JakeBoothy/PhotoSpectrometer-Electrical/V2/Eagle/LTSpice/amp_test.asc

R1: res; 10k
R2: res; 2408
R3: res; 201
R4: res; 600
R5: res; 100k
R6: res; 2.7k
R7: res; 10k
R8: res; 500
R9: res; 1.7k
R10: res; 100k
U1: ADA4807
U2: ADA4807
U3: ADA4807
V1: voltage; 5
V2: voltage; -5
V3: voltage; SINE(1.55 0.95 2e4)
V4: voltage; 2.5
Named nets: 0, +5, -5, +2.5
.tran 1
