JakeBoothy/PhotoSpectrometer-Electrical/V2/Eagle/LTSpice/CurrentSense.asc

R1: res; 10k
R2: res; 60k
R3: res; 2k
R4: res; 60k
R5: res; 0.05
R6: res; 2.5
U1: LM358
V1: voltage; 3.3
V2: voltage; PWL(0 0 1 20)
Named nets: 0, 3.3V, 12V
.tran 1
.inc LM358.MOD
