JakeBoothy/PhotoSpectrometer-Electrical/V2/Eagle/LTSpice/Draft2.asc

C1: cap; 200nF
M1: nmos; IRF8721
Q1: npn
R1: res; 51k
R2: res; 51k
R3: res; 10
V1: voltage; PULSE(0 36 0 0 0 0.05 0.1 10)
V2: voltage; 3.7
V3: voltage; 12V
Named nets: 0, 3.7V, 12V
.tran 1
