JakeBoothy/PhotoSpectrometer-Electrical/V2/Eagle/LTSpice/Draft3.asc

2.5k: res; 25k
R2: res; 10k
R3: res; 100k
R4: res; 80k
U1: UniversalOpamp2
V1: voltage; 2.5
V2: voltage; -2.5
V3: voltage; SINE(1.55 0.95 1E3)
Named nets: 0, +2.5V, -2.5V
.tran 1e-2
