JakeBoothy/PhotoSpectrometer-Electrical/V2/Eagle/LTSpice/Pelt_Driver.asc

C1: cap; 47µ
D1: diode
L1: ind; 100µ
M1: nmos; Si7336ADP
R1: res; 2.5
V1: voltage; 12V
V2: voltage; PULSE(0 3.3 0 0 0 0.00005 0.0001)
Named nets: 0
.tran 0.01
