JakeBoothy/PhotoSpectrometer-Electrical/V2/LTSPICE/LM358/Draft1.asc

R2: res; 10k
R3: res; 10k
U1: LM358
V1: voltage; 5
V2: voltage; SINE(1.5 1 5)
Named nets: 0
.tran 1
.inc LM358.MOD
