JakeBoothy/PhotoSpectrometer-Electrical/V2/Eagle/LTSpice/Draft1.asc

Q1: npn; 2SCR514P
R1: res; 51k
R2: res; 51k
R3: res; 120k
V1: voltage; PULSE(0 36 0 0 0 0.05 0.1)
V2: voltage; 4.2
Named nets: 0
.tran 0.2
