JakeBoothy/PhotoSpectrometer-Electrical/V2/Eagle/ccd_driver.sch

## EAGLE design V2/Eagle/ccd_driver.sch (2018-10-21)

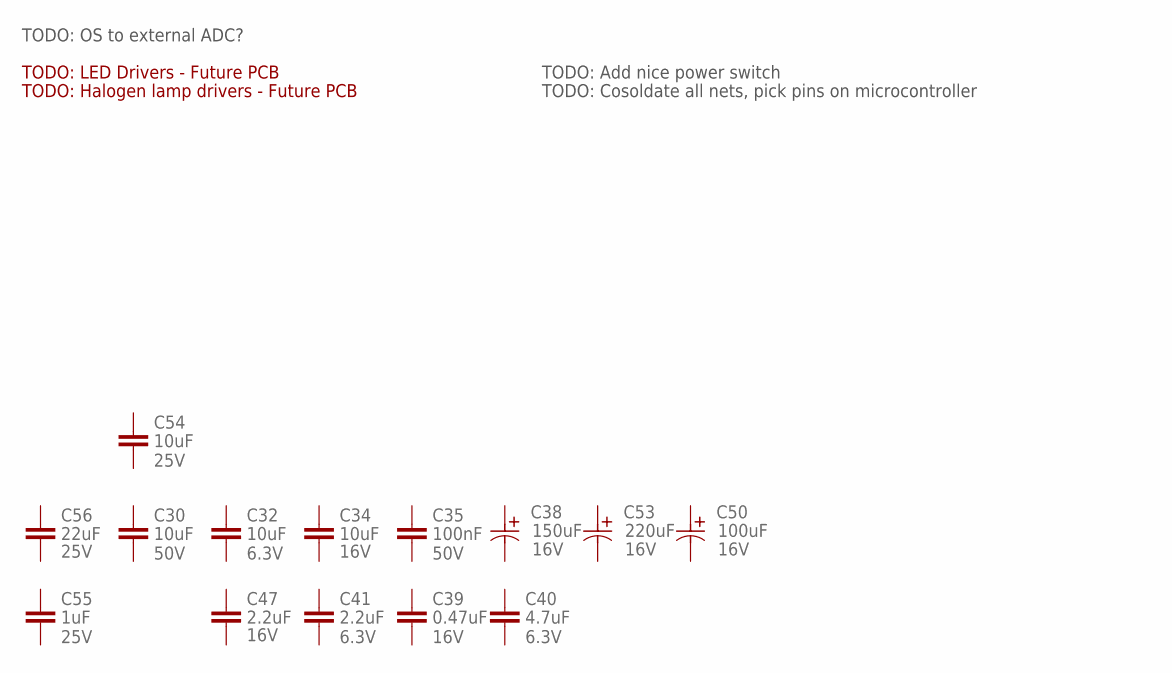
[picture p5: schematic ccd_driver.sch, sheet 1]

Parts:
C30: 10uF; C1206; VOLTAGE 50V; PARTNO 490-12456-1-ND
C32: 10uF; 0603-CAP; VOLTAGE 6.3V; PARTNO 1276-1119-1-ND
C34: 10uF; C0805; VOLTAGE 16V; PARTNO 1276-1096-1-ND
C35: 100nF; 0603-CAP; VOLTAGE 50V; PARTNO 311-1343-1-ND
C38: UWZ1C151MCL1GS; PCAP_6.3X7.7-ELECT; VOLTAGE 16V
C39: 0.47uF; 0603-CAP; VOLTAGE 16V; PARTNO 1276-1062-1-ND
C40: 4.7uF; 0603-CAP; VOLTAGE 6.3V; PARTNO 1276-1045-1-ND
C41: 2.2uF; 0603-CAP; VOLTAGE 6.3V; PARTNO 445-6933-1-ND
C47: 2.2uF; C0805; VOLTAGE 16V; PARTNO 1276-2957-1-ND
C50: EMVE160ADA101MF55G; PCAP_6.3X7.7-ELECT; VOLTAGE 16V
C53: UWZ1C151MCL1GS; PCAP_6.3X7.7-ELECT; VOLTAGE 16V; MANUFACTURER_PART_NUMBER UWT1C221MCL1GS
C54: 10uF; C1206; VOLTAGE 25V; PARTNO 1276-1075-1-ND
C55: 1uF; 0603-CAP; VOLTAGE 25V; PARTNO 1276-1102-1-ND
C56: 22uF; C0805; VOLTAGE 25V; PARTNO 490-12389-1-ND

Notes on the sheet:
TODO: OS to external ADC?
TODO: LED Drivers - Future PCB
TODO: Halogen lamp drivers - Future PCB
TODO: Add nice power switch
TODO: Cosoldate all nets, pick pins on microcontroller

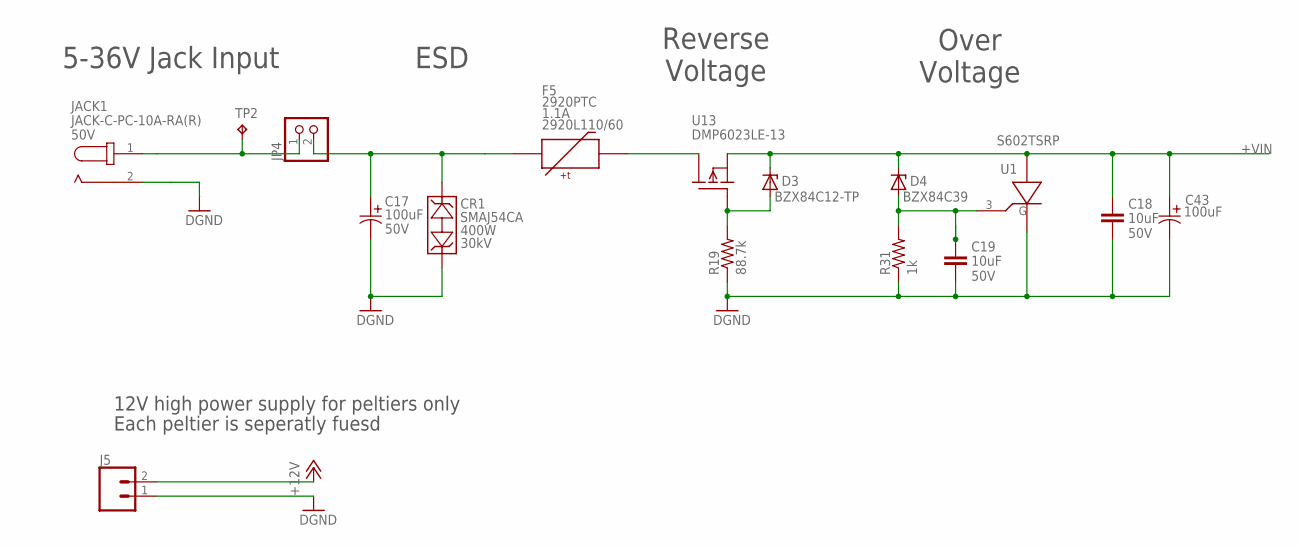
[picture p6: schematic ccd_driver.sch, sheet 2]

Parts:
C17: UWT1H101MNL1GS; PCAP_8X10-ELECT; VOLTAGE 50V
C18, C19: 10uF; C1206; VOLTAGE 50V; PARTNO 490-12456-1-ND
C43: UWT1H101MNL1GS; PCAP_8X10-ELECT
CR1: SMAJ54CA; SMASERIES
D3: BZX84C12-TP; SOT23
D4: BZX84C39; SOT23
F5: 2920PTC; 2920; PARTNO 2920L110/60
J5: CONN_023.5MM; SCREWTERMINAL-3.5MM-2
JACK1: JACK-C-PC-10A-RA(R); 1939-1086-ND
JP4: PINHD-1X2; 1X02
R19: 88.7k; R0603
R31: 1k; R0603
TP2: TPPAD1-13; P1-13
U1: S602TSRP; SOT223
U13: DMP6023LE-13; SOT-223

Connections:
+12V: J5.2
+VIN: C18.1, C43.1 (11), D3.3 (C), D4.3 (C), U1.2 (A), U13.3 (S)
GND: C17.2 (22), C18.2, C19.2, C43.2 (22), CR1.2 (1), J5.1, JACK1.2, R19.1, R31.1, U1.1 (K)
unnamed: C17.1 (11), CR1.1 (2), F5.P$2, JP4.2
unnamed: JACK1.1, JP4.1, TP2.TP
unnamed: F5.P$1, U13.2 (D)
unnamed: D3.1 (A), R19.2, U13.1 (G)
unnamed: C19.1, D4.1 (A), R31.2, U1.3 (G)

Notes on the sheet:
ESD
Reverse Voltage
Over Voltage
Each peltier is seperatly fuesd
5-36V Jack Input
12V high power supply for peltiers only

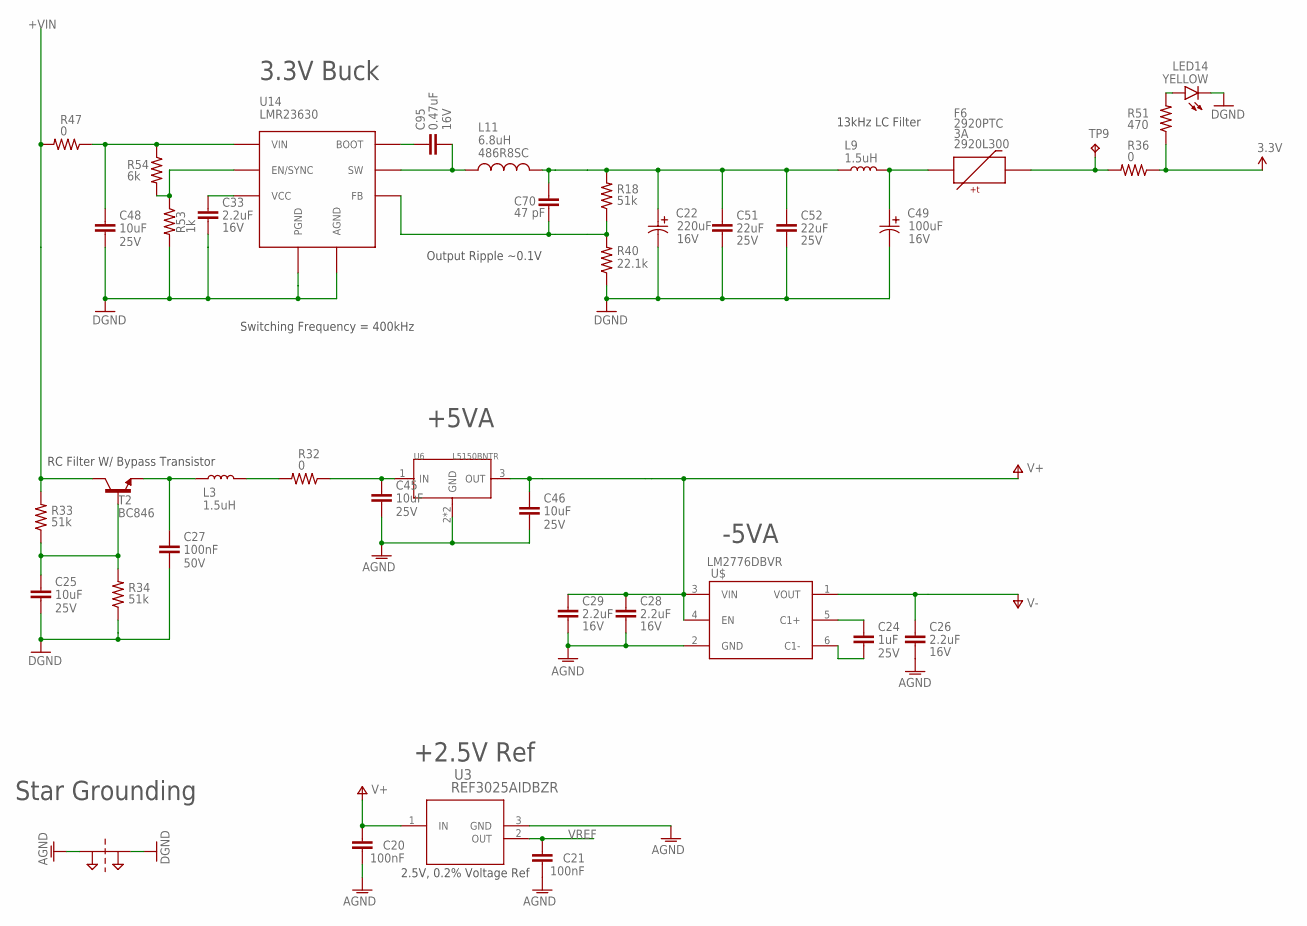
[picture p7: schematic ccd_driver.sch, sheet 3]

Parts:
C20, C21: 100nF; 0603-CAP
C22: UWZ1C151MCL1GS; PCAP_6.3X7.7-ELECT; VOLTAGE 16V; MANUFACTURER_PART_NUMBER UWT1C221MCL1GS
C24: 1uF; 0603-CAP; VOLTAGE 25V; PARTNO 1276-1102-1-ND
C25, C45, C46, C48: 10uF; C1206; VOLTAGE 25V; PARTNO 1276-1075-1-ND
C26, C28, C29, C33: 2.2uF; C0805; VOLTAGE 16V; PARTNO 1276-2957-1-ND
C27: 100nF; 0603-CAP; VOLTAGE 50V; PARTNO 311-1343-1-ND
C49: EMVE160ADA101MF55G; PCAP_6.3X7.7-ELECT; VOLTAGE 16V
C51, C52: 22uF; C0805; VOLTAGE 25V; PARTNO 490-12389-1-ND
C70: 47 pF; 0603-CAP
C95: 0.47uF; 0603-CAP; VOLTAGE 16V; PARTNO 1276-1062-1-ND
F6: 2920PTC; 2920; PARTNO 2920L300
L3, L9: CIGW252010GLR47MNE; 2520
L11: 486R8SC
LED14: SML-LX23; 3X2SMDLED
R18, R33, R34: 51k; R0603
R32, R36, R47: 0; R0603
R40: 22.1k; R0603
R51: 470; R0603
R53: 1k; R0603
R54: 6k; R0603
SUPPLY21: 2PT_GND_TIE
T2: BC846; SOT23
TP9: TPPAD1-13; P1-13
U3: REF3025AIDBZR; DBZ3
U6: L5150BNTR; SOT-223
U14: LMR23630; HSOIC-8
U$: LM2776DBVR; SOT23-6

Connections:
3.3V: R36.1, R51.1
+VIN: R33.2, R47.2, T2.3 (C)
AGND: C20.2, C21.2, C26.2, C28.2, C29.2, C45.2, C46.2, SUPPLY21.P$1, U3.3 (GND), U6.2 (GND), U$.2 (GND)
GND: C22.2 (22), C25.2, C27.2, C33.2, C48.2, C49.2 (22), C51.2, C52.2, LED14.C, R34.1, R40.1, R53.2, SUPPLY21.P$2, U14.P$6 (AGND), U14.P$8 (PGND)
unnamed: C45.1, R32.1, U6.1 (IN)
unnamed: L3.2, R32.2
unnamed: C25.1, R33.1, R34.2, T2.1 (B)
unnamed: C27.1, L3.1, T2.2 (E)
unnamed: C33.1, U14.P$3 (VCC)
unnamed: R53.1, R54.2, U14.P$5 (EN/SYNC)
unnamed: C48.1, R47.1, R54.1, U14.P$7 (VIN)
unnamed: C70.2, R18.1, R40.2, U14.P$4 (FB)
unnamed: C95.2, L11.P$1 (1), U14.P$1 (SW)
unnamed: C95.1, U14.P$2 (BOOT)
unnamed: C22.1 (11), C51.1, C52.1, C70.1, L9.1, L11.P$2 (2), R18.2
unnamed: F6.P$1, R36.2, TP9.TP
unnamed: LED14.A, R51.2
unnamed: C24.1, U$.5 (C1+)
unnamed: C24.2, U$.6 (C1-)
unnamed: C49.1 (11), F6.P$2, L9.2
V+: C20.1, C28.1, C29.1, C46.1, U3.1 (IN), U6.3 (OUT), U$.3 (VIN), U$.4 (EN)
V-: C26.1, U$.1 (VOUT)
VREF: C21.1, U3.2 (OUT)

Notes on the sheet:
2.5V, 0.2% Voltage Ref
13kHz LC Filter
Output Ripple ~0.1V
Switching Frequency = 400kHz
RC Filter W/ Bypass Transistor
3.3V Buck
+5VA
-5VA
+2.5V Ref
Star Grounding

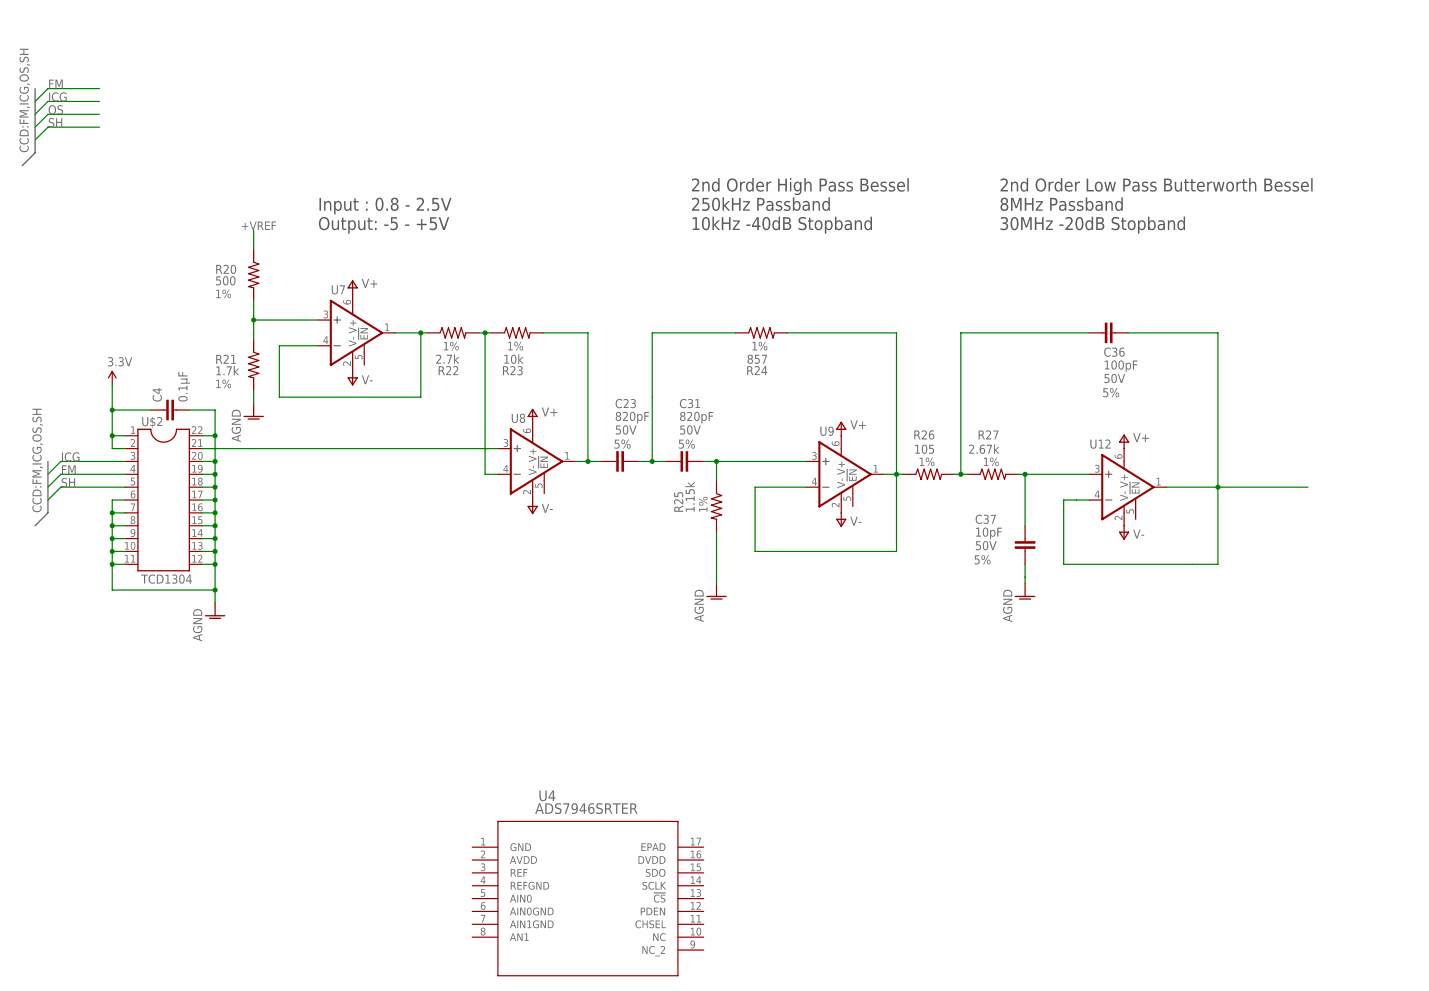
[picture p8: schematic ccd_driver.sch, sheet 4]

Parts:
C4: 0.1µF; C1206
C23, C31: 820pF; 0603-CAP; TOLERANCE 5%; VOLTAGE 50V; PARTNO 311-1343-1-ND
C36: 100pF; 0603-CAP; TOLERANCE 5%; VOLTAGE 50V; PARTNO 311-1343-1-ND
C37: 10pF; 0603-CAP; TOLERANCE 5%; VOLTAGE 50V; PARTNO 311-1343-1-ND
R20: 500; R0603; TOLERANCE 1%
R21: 1.7k; R0603; TOLERANCE 1%
R22: 2.7k; R0603; TOLERANCE 1%
R23: 10k; R0603; TOLERANCE 1%
R24: 857; R0603; TOLERANCE 1%
R25: 1.15k; R0603; TOLERANCE 1%
R26: 105; R0603; TOLERANCE 1%
R27: 2.67k; R0603; TOLERANCE 1%
U4: ADS7946SRTER; RTE16_1P7X1P7
U7, U8, U9, U12: ADA4807-1ARJZ-R2; RJ_6
U$2: TCD1304

Connections:
3.3V: C4.1, U$2.1, U$2.2
+VREF: R20.1
AGND: C4.2, C37.1, R21.2, R25.2, U$2.6, U$2.7, U$2.8, U$2.9, U$2.10, U$2.11, U$2.12, U$2.13, U$2.14, U$2.15, U$2.16, U$2.17, U$2.18, U$2.19, U$2.20, U$2.22
FM: U$2.4
ICG: U$2.3
unnamed: U8.3 (+IN), U$2.21
unnamed: R20.2, R21.1, U7.3 (+IN)
unnamed: R22.1, U7.1 (OUT), U7.4 (-IN)
unnamed: R22.2, R23.1, U8.4 (-IN)
unnamed: C23.1, R23.2, U8.1 (OUT)
unnamed: C23.2, C31.1, R24.1
unnamed: C31.2, R25.1, U9.3 (+IN)
unnamed: R24.2, R26.1, U9.1 (OUT), U9.4 (-IN)
unnamed: C37.2, R27.2, U12.3 (+IN)
unnamed: C36.1, R26.2, R27.1
unnamed: C36.2, U12.1 (OUT), U12.4 (-IN)
SH: U$2.5
V+: U7.6 (V+), U8.6 (V+), U9.6 (V+), U12.6 (V+)
V-: U7.2 (V-), U8.2 (V-), U9.2 (V-), U12.2 (V-)

Notes on the sheet:
Input : 0.8 - 2.5V Output: -5 - +5V
2nd Order High Pass Bessel 250kHz Passband 10kHz -40dB Stopband
2nd Order Low Pass Butterworth Bessel 8MHz Passband 30MHz -20dB Stopband

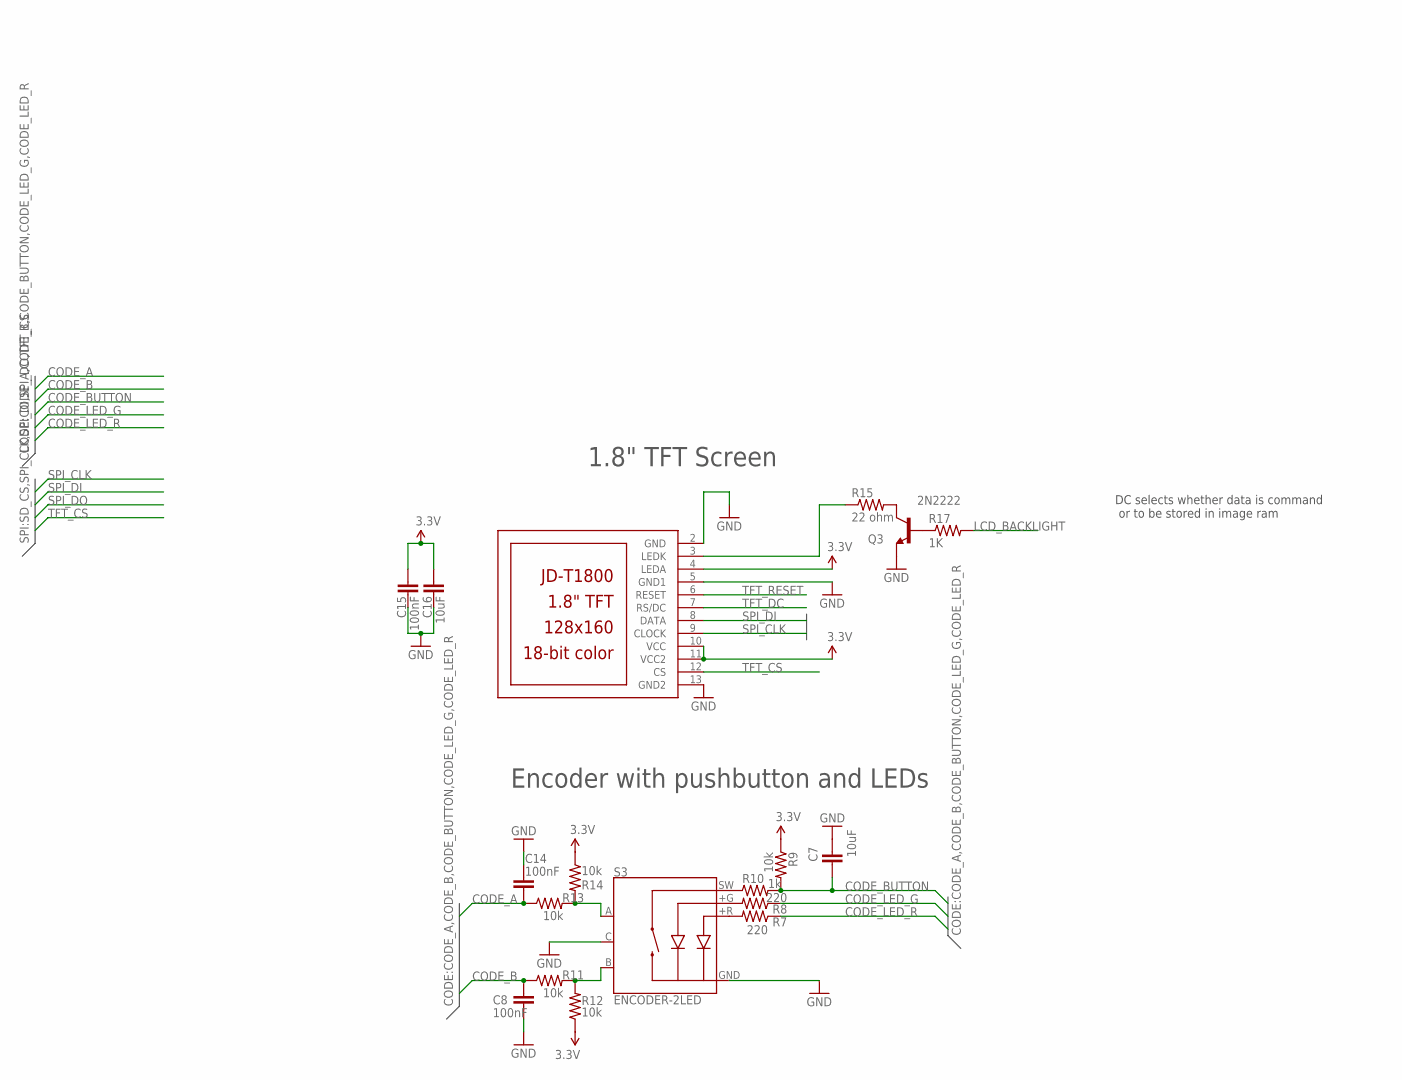
[picture p9: schematic ccd_driver.sch, sheet 5]

Parts:
C7, C16: 10uF; 0603-CAP
C8, C14, C15: 100nF; 0603-CAP
Q3: 2N2222; SOT23-BEC
R7, R8: 220; R0603
R9, R11, R12, R13, R14: 10k; R0603
R10: 1k; R0603
R15: 22 ohm; R0805
R17: 1K; R0805
S3: ENCODER-2LED; ENCODER_LED_2
U$10: JD-T1800

Connections:
3.3V: C15.1, C16.1, R9.1, R12.1, R14.1, U$10.4 (LEDA), U$10.10 (VCC), U$10.11 (VCC2)
CODE_A: C14.2, R13.1
CODE_B: C8.1, R11.1
CODE_BUTTON: C7.2, R9.2, R10.2
CODE_LED_G: R8.1
CODE_LED_R: R7.1
GND: C7.1, C8.2, C14.1, C15.2, C16.2, Q3.E, S3.C, S3.GND (-), U$10.2 (GND), U$10.5 (GND1), U$10.13 (GND2)
LCD_BACKLIGHT: R17.2
unnamed: R7.2, S3.+R
unnamed: R8.2, S3.+G
unnamed: R10.1, S3.SW
unnamed: R13.2, R14.2, S3.A
unnamed: R11.2, R12.2, S3.B
unnamed: R15.1, U$10.3 (LEDK)
unnamed: Q3.C, R15.2
unnamed: Q3.B, R17.1
SPI_CLK: U$10.9 (CLOCK)
SPI_DI: U$10.8 (DATA)
TFT_CS: U$10.12 (CS)
TFT_DC: U$10.7 (RS/DC)
TFT_RESET: U$10.6 (RESET)

Notes on the sheet:
DC selects whether data is command or to be stored in image ram
1.8" TFT Screen
Encoder with pushbutton and LEDs

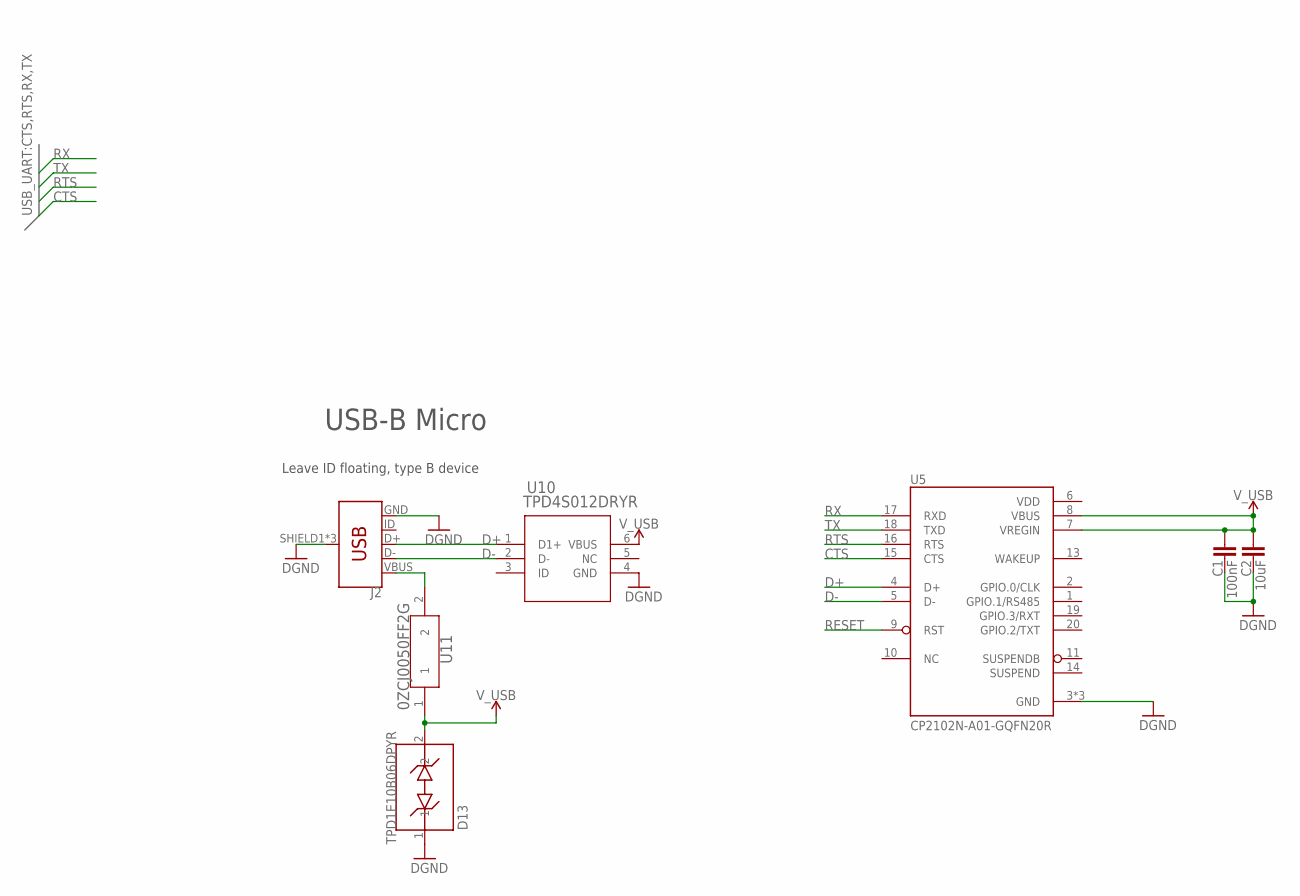
[picture p10: schematic ccd_driver.sch, sheet 6]

Parts:
C1: 100nF; 0603-CAP
C2: 10uF; 0603-CAP
D13: TPD1E10B06DPYR; DFN100X60X45-2N
J2: USB_MICRO-B_FEMALE-SMT; USB-B-MICRO-SMD
U5: CP2102N-A01-GQFN20R; SILABS_QFN20
U10: TPD4S012DRYR; DRY6
U11: 0ZCJ0050FF2G; 0ZCJ

Connections:
CTS: U5.15 (CTS)
D+: J2.D+, U5.4 (D+), U10.1 (D1+)
D-: J2.D-, U5.5 (D-), U10.2 (D-)
GND: C1.2, C2.2, D13.1, J2.GND, J2.SHIELD1 (SHIELD), U5.3 (GND), U10.4 (GND)
unnamed: J2.VBUS, U11.2
RESET: U5.9 (RST)
RTS: U5.16 (RTS)
RX: U5.17 (RXD)
TX: U5.18 (TXD)
V_USB: C1.1, C2.1, D13.2, U5.7 (VREGIN), U5.8 (VBUS), U10.6 (VBUS), U11.1

Notes on the sheet:
Leave ID floating, type B device
USB-B Micro

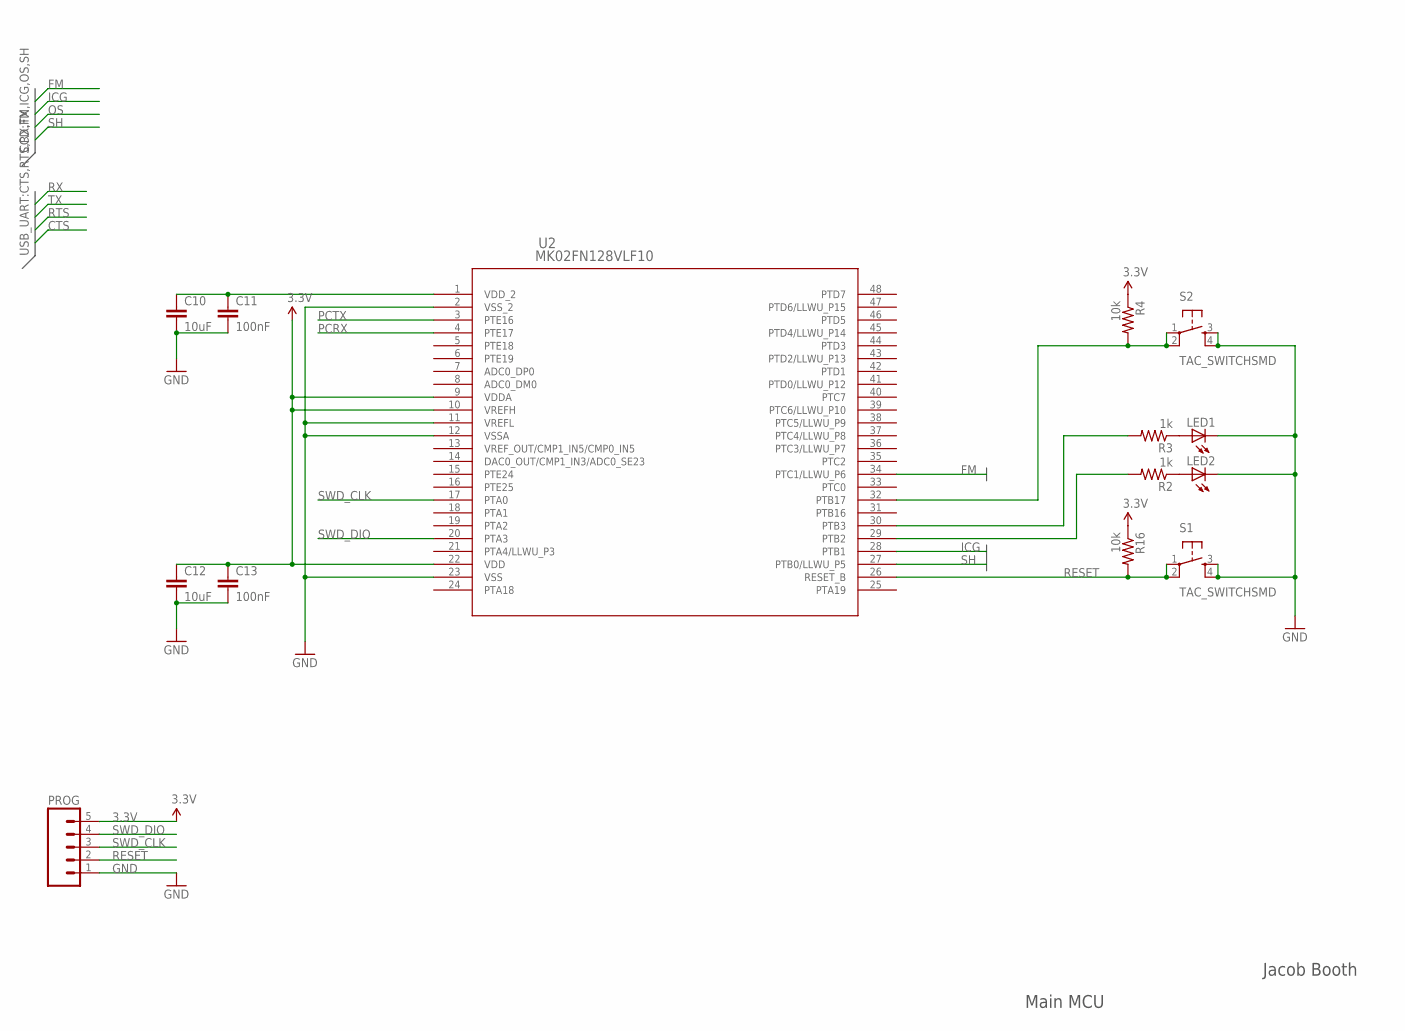
[picture p11: schematic ccd_driver.sch, sheet 7]

Parts:
C10, C12: 10uF; 0603
C11, C13: 100nF; 0603
LED1, LED2: LEDCHIPLED_0805; CHIPLED_0805
PROG: M05LOCK; 1X05_LOCK
R2, R3: 1k; R0603
R4, R16: 10k; R0603
S1, S2: TAC_SWITCHSMD; TACTILE-SWITCH-SMD
U2: MK02FN128VLF10; LQFP-48_7X7X1.6

Connections:
3.3V: C12.1, C13.1, PROG.5, R4.1, R16.1, U2.9 (VDDA), U2.10 (VREFH), U2.22 (VDD)
FM: U2.34 (PTC1/LLWU_P6)
GND: C10.2, C11.2, C12.2, C13.2, LED1.C, LED2.C, PROG.1, S1.3, S1.4, S2.3, S2.4, U2.2 (VSS_2), U2.11 (VREFL), U2.12 (VSSA), U2.23 (VSS)
ICG: U2.28 (PTB1)
unnamed: R4.2, S2.1, S2.2, U2.32 (PTB17)
unnamed: R3.2, U2.30 (PTB3)
unnamed: LED1.A, R3.1
unnamed: R2.2, U2.29 (PTB2)
unnamed: LED2.A, R2.1
unnamed: C10.1, C11.1, U2.1 (VDD_2)
PCRX: U2.4 (PTE17)
PCTX: U2.3 (PTE16)
RESET: PROG.2, R16.2, S1.1, S1.2, U2.26 (RESET_B)
SH: U2.27 (PTB0/LLWU_P5)
SWD_CLK: PROG.3, U2.17 (PTA0)
SWD_DIO: PROG.4, U2.20 (PTA3)

Notes on the sheet:
Main MCU
Jacob Booth

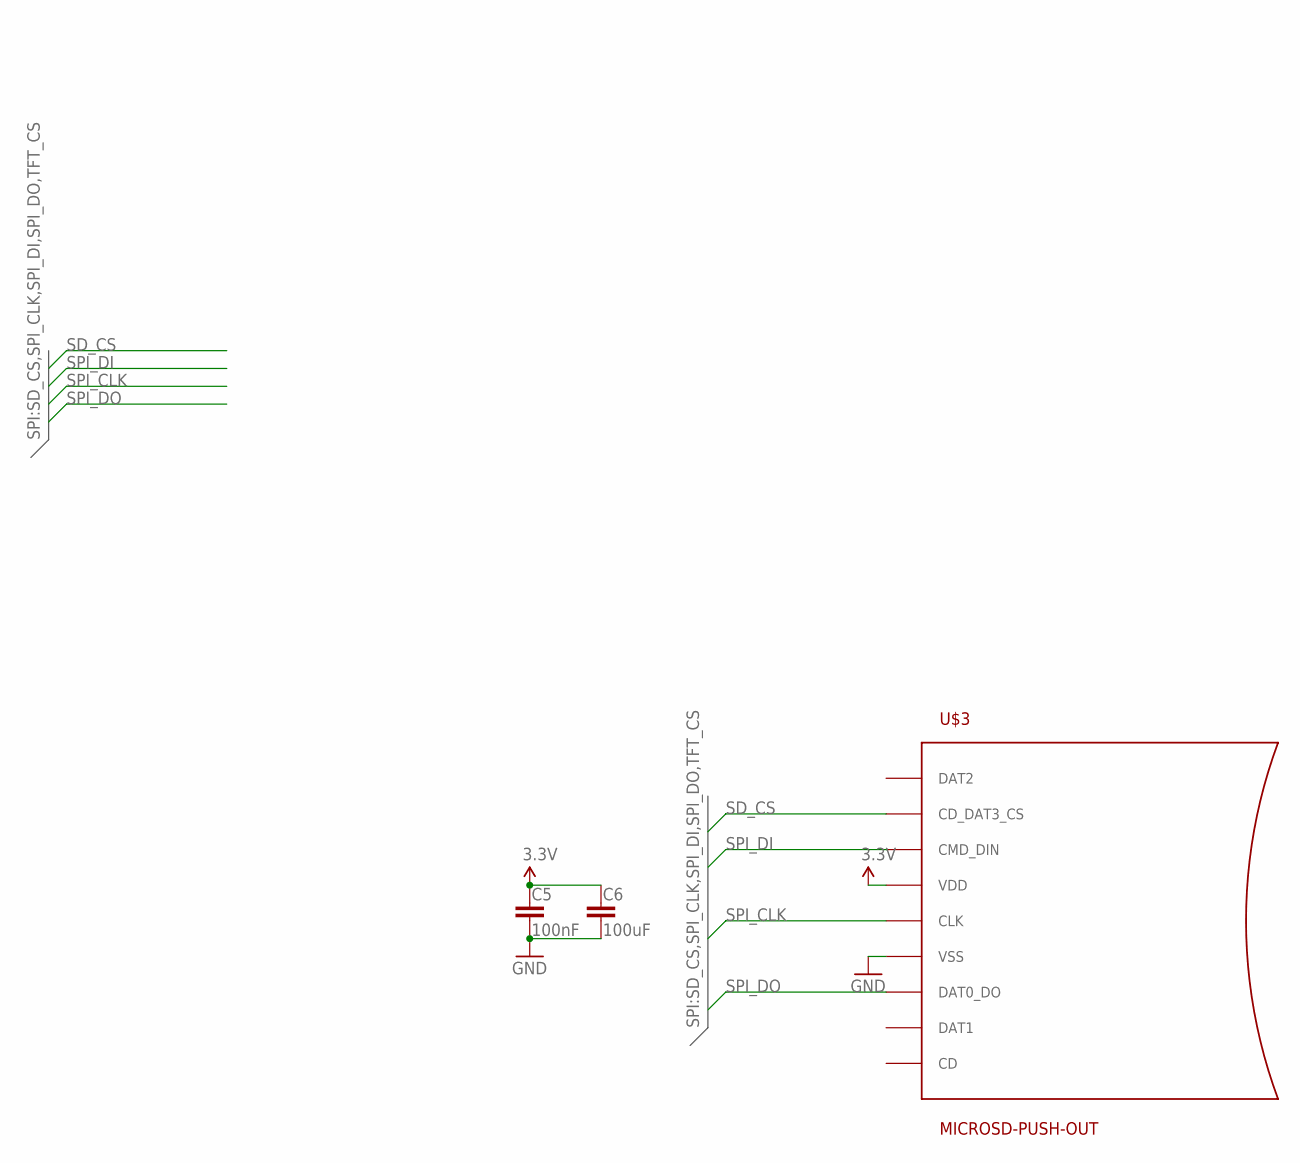
[picture p12: schematic ccd_driver.sch, sheet 8]

Parts:
C5: 100nF; 0603-CAP
C6: 100uF; 0603-CAP
U$3: MICROSD-PUSH-OUT

Connections:
3.3V: C5.1, C6.1, U$3.4 (VDD)
GND: C5.2, C6.2, U$3.6 (VSS)
SD_CS: U$3.2 (CD_DAT3_CS)
SPI_CLK: U$3.5 (CLK)
SPI_DI: U$3.3 (CMD_DIN)
SPI_DO: U$3.7 (DAT0_DO)

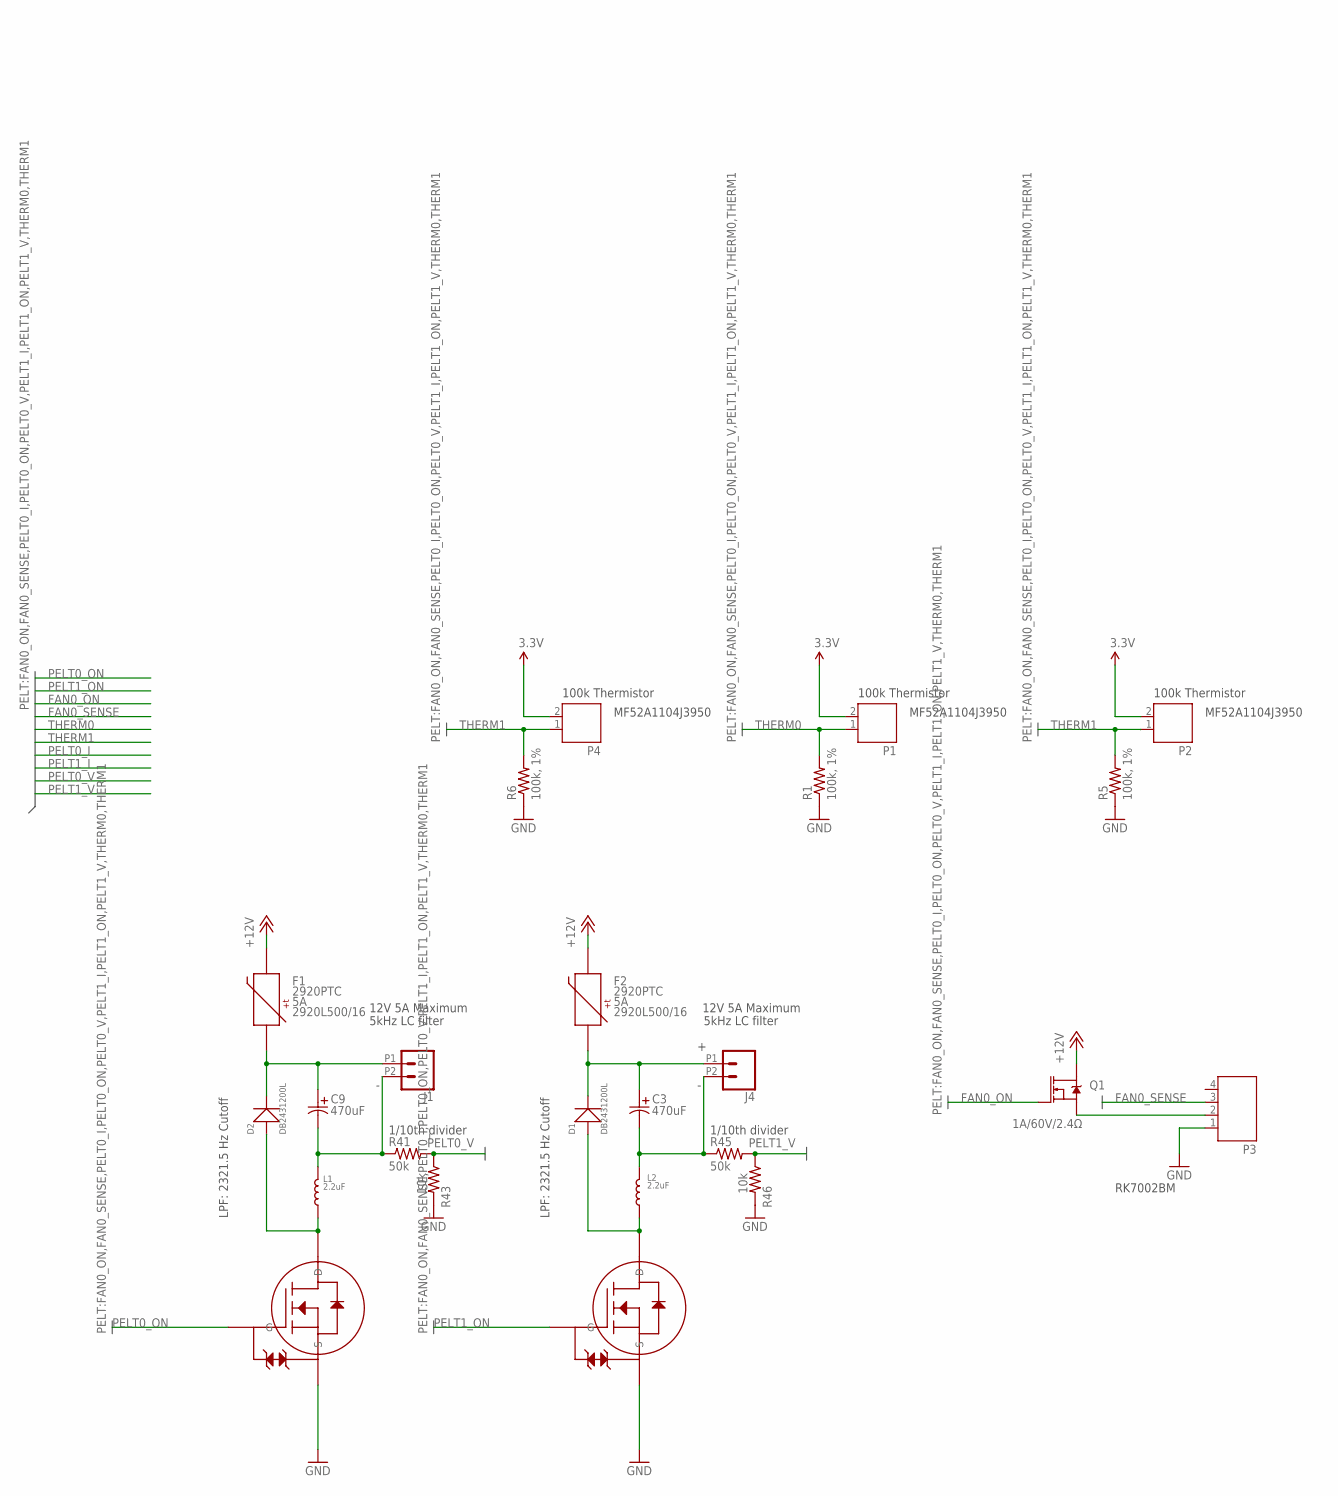
[picture p13: schematic ccd_driver.sch, sheet 9]

Parts:
C3, C9: 470uF; PCAP_8X10-ELECT
D1, D2: DB2431200L
F1, F2: 2920PTC; 2920; PARTNO 2920L500/16
J1, J4: CONN_022.54MM_SCREWTERM; 1X02_2.54_SCREWTERM
L1, L2: 2.2uF; VLS6045EX
P1, P2, P4: JST-PH2
P3: JST-PH4
Q1: 1A/60V/2.4Ω; SOT23-3
R1, R5, R6: 100k, 1%; R0603
R41, R45: 50k; R0603
R43, R46: 10k; R0603
U$1, U$4: DMN1019UVT; TSOT26

Connections:
3.3V: P1.2, P2.2, P4.2
+12V: F1.P$1, F2.P$1, Q1.3 (D)
FAN0_ON: Q1.1 (G)
FAN0_SENSE: P3.3
GND: P3.1, R1.1, R5.1, R6.1, R43.2, R46.2, U$1.P$4 (S), U$4.P$4 (S)
unnamed: C3.2 (22), J4.P2 (2), L2.2, R45.1
unnamed: D1.P$1 (+), L2.1, U$1.P$1 (D)
unnamed: P3.2, Q1.2 (S)
unnamed: C9.2 (22), J1.P2 (2), L1.2, R41.1
unnamed: D2.P$1 (+), L1.1, U$4.P$1 (D)
unnamed: C9.1 (11), D2.P$2 (-), F1.P$2, J1.P1 (1)
unnamed: C3.1 (11), D1.P$2 (-), F2.P$2, J4.P1 (1)
PELT0_ON: U$4.P$3 (G)
PELT0_V: R41.2, R43.1
PELT1_ON: U$1.P$3 (G)
PELT1_V: R45.2, R46.1
THERM0: P1.1, R1.2
THERM1: P2.1, P4.1, R5.2, R6.2

Notes on the sheet:
LPF: 2321.5 Hz Cutoff
12V 5A Maximum
RK7002BM
100k Thermistor
MF52A1104J3950
1/10th divider
5kHz LC filter
